Darkextratoasty/Mini-MediaPad/pictures/PXL_20230915_193252561.jpg

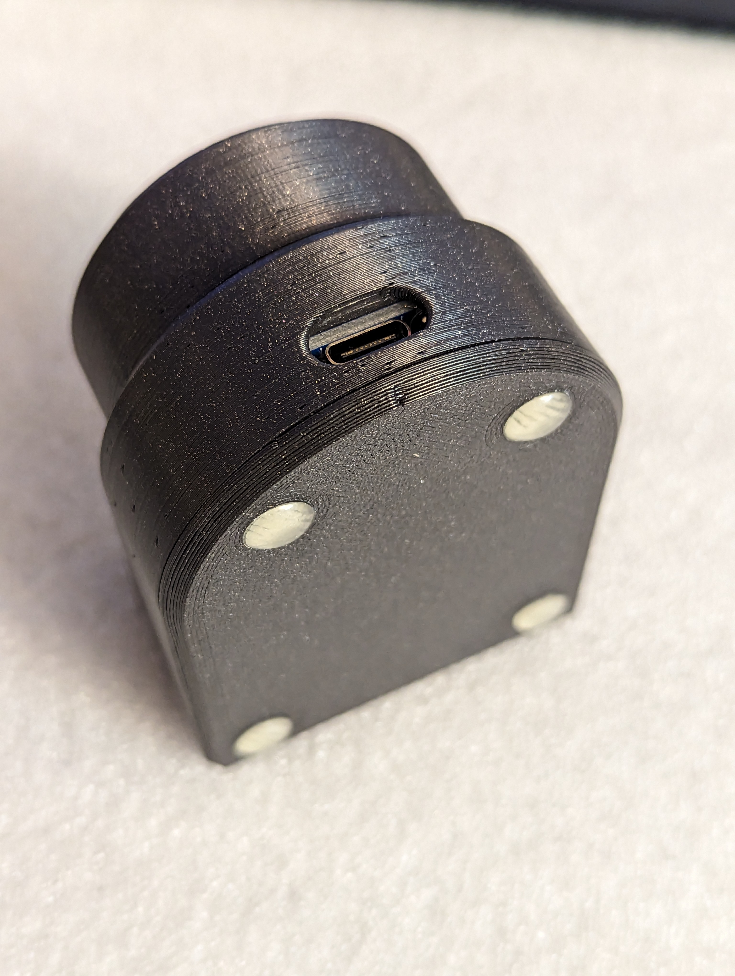
pictures/PXL_20230915_193252561.jpg
