Darkextratoasty/Mini-MediaPad/pictures/PXL_20230915_193416672.jpg

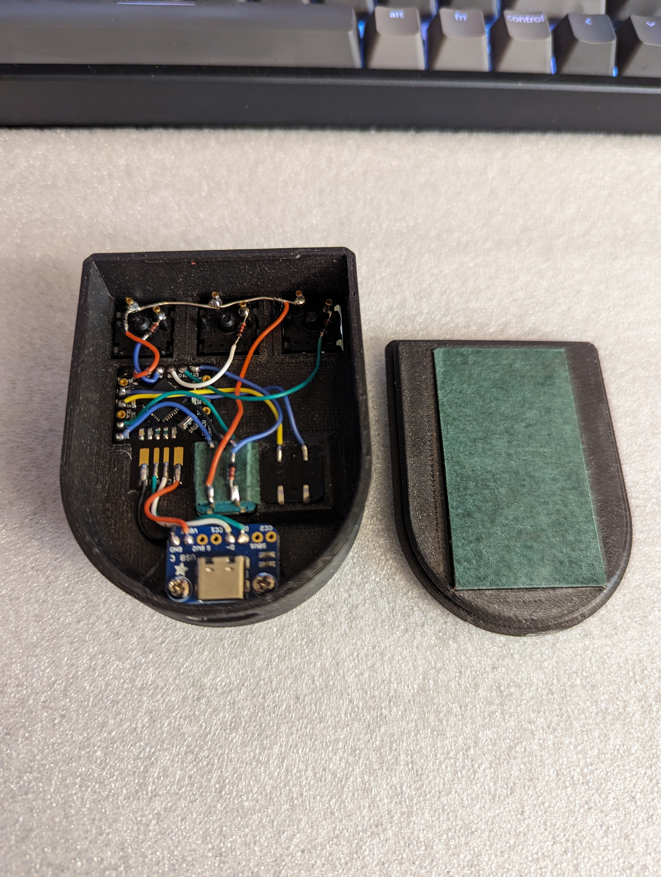
pictures/PXL_20230915_193416672.jpg
