Darkextratoasty/Mini-MediaPad/pictures/PXL_20230915_193520012.jpg

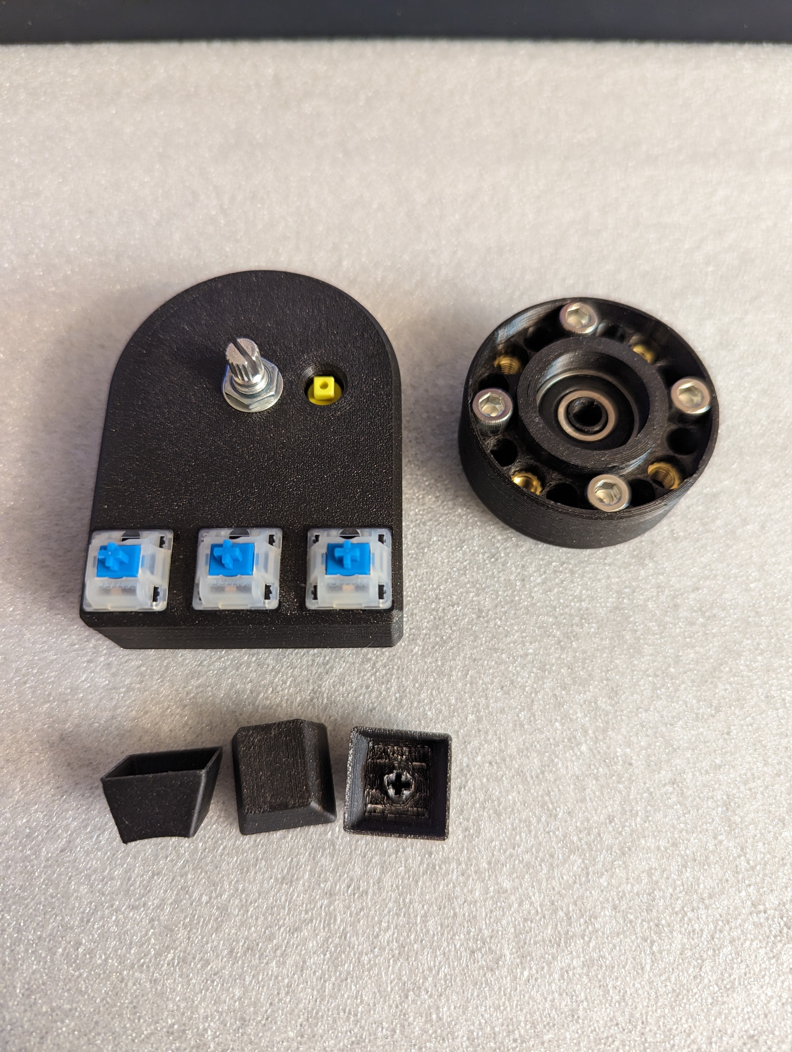
pictures/PXL_20230915_193520012.jpg
