Darkextratoasty/Mini-MediaPad/pictures/PXL_20230915_193528112.jpg

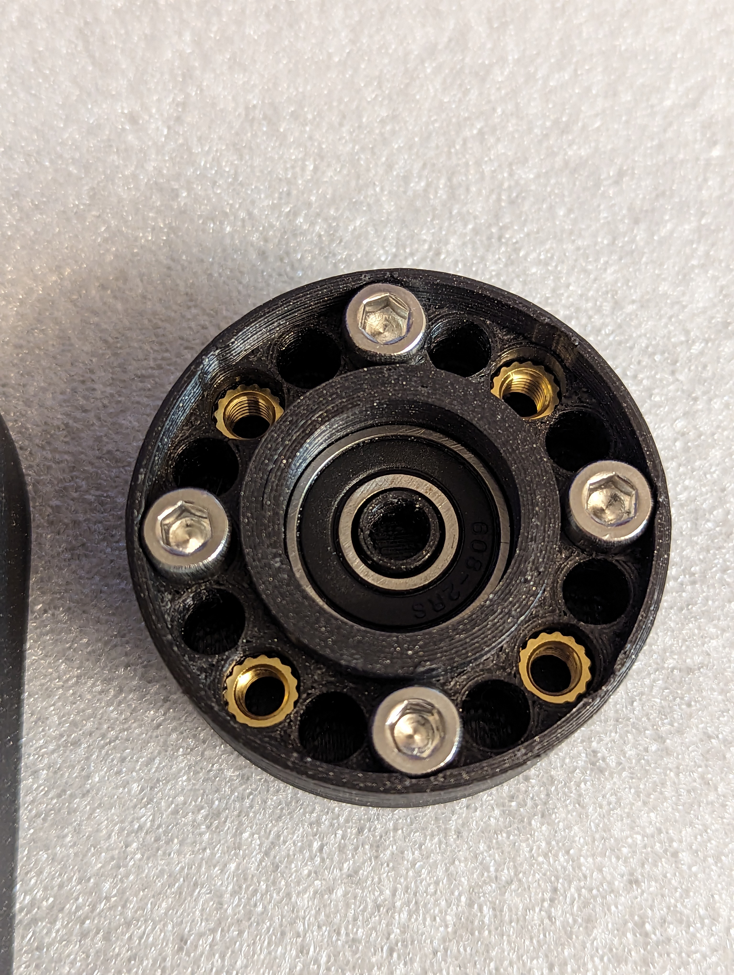
pictures/PXL_20230915_193528112.jpg
